mehtaheino/MANU-3D-Printer/Assets - Images for Documentation/0002-Accessories-100-1.jpg

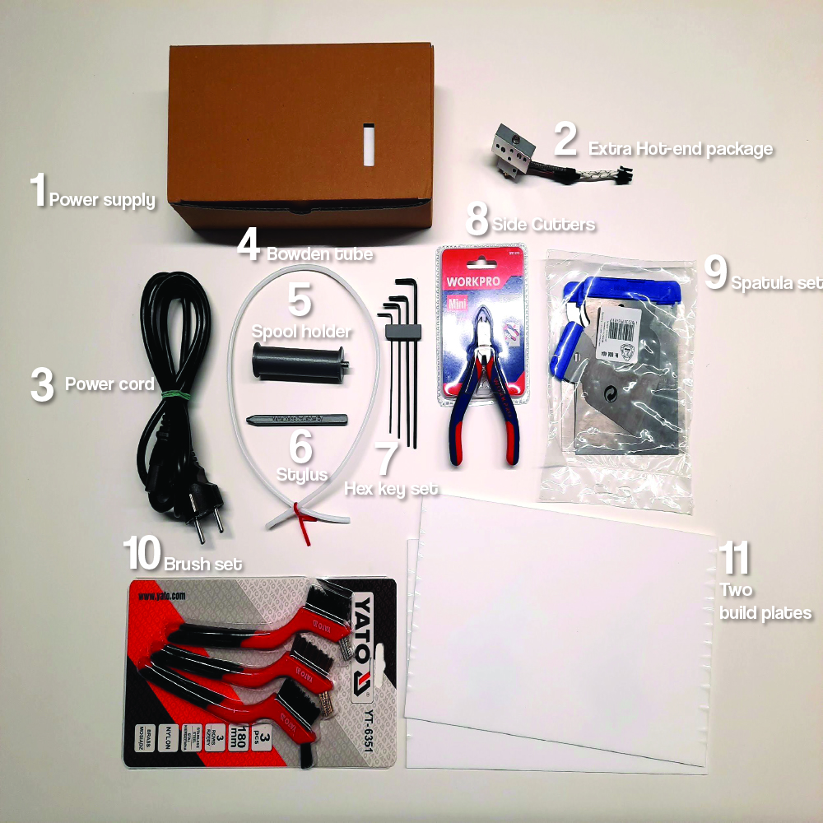
Assets - Images for Documentation/0002-Accessories-100-1.jpg
