mehtaheino/MANU-3D-Printer/Assets - Images for Documentation/About Creating STL files.png

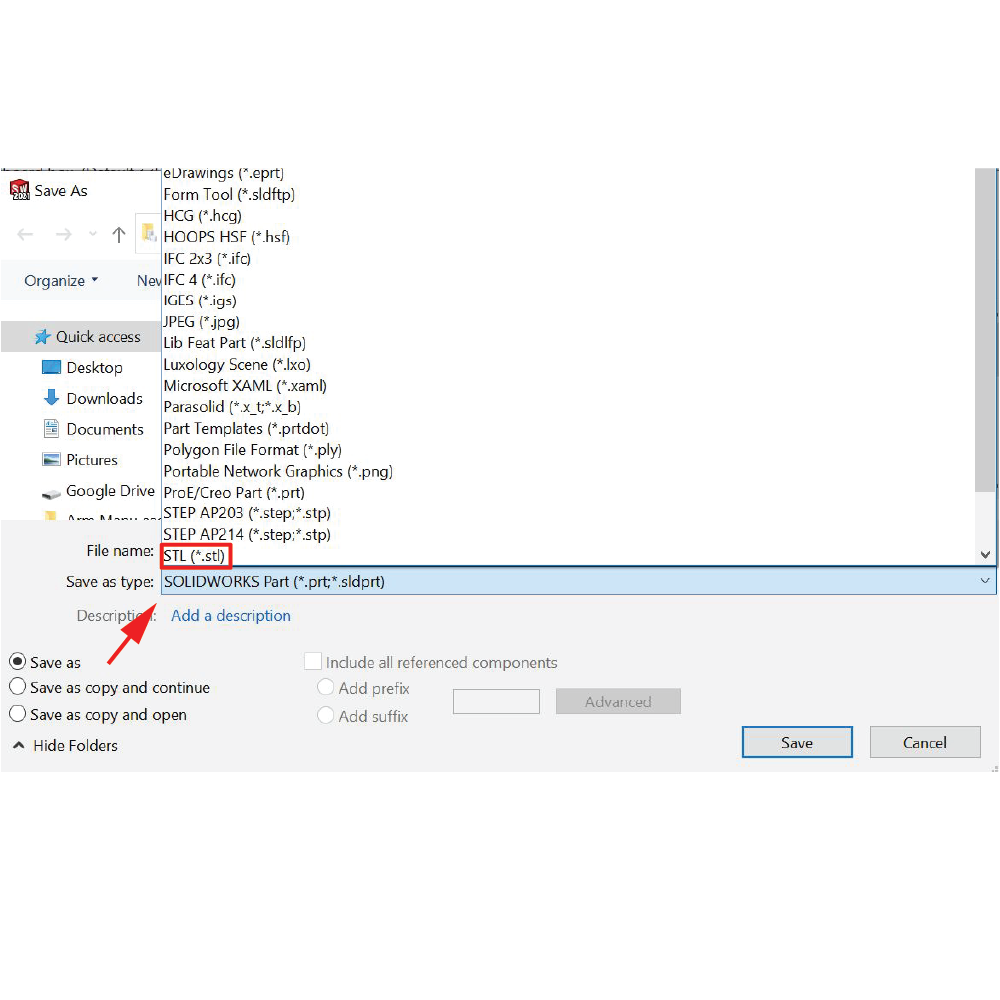
Assets - Images for Documentation/About Creating STL files.png
