mehtaheino/MANU-3D-Printer/Assets - Images for Documentation/Accessories.png

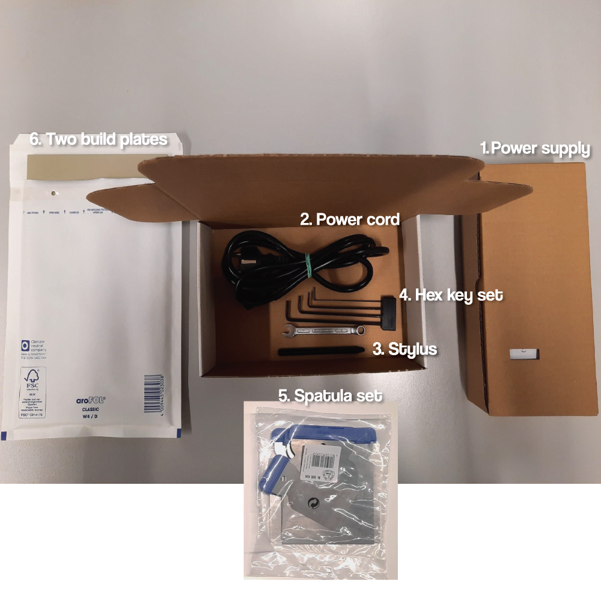
Assets - Images for Documentation/Accessories.png
