mehtaheino/MANU-3D-Printer/Assets - Images for Documentation/Choose the profile.png

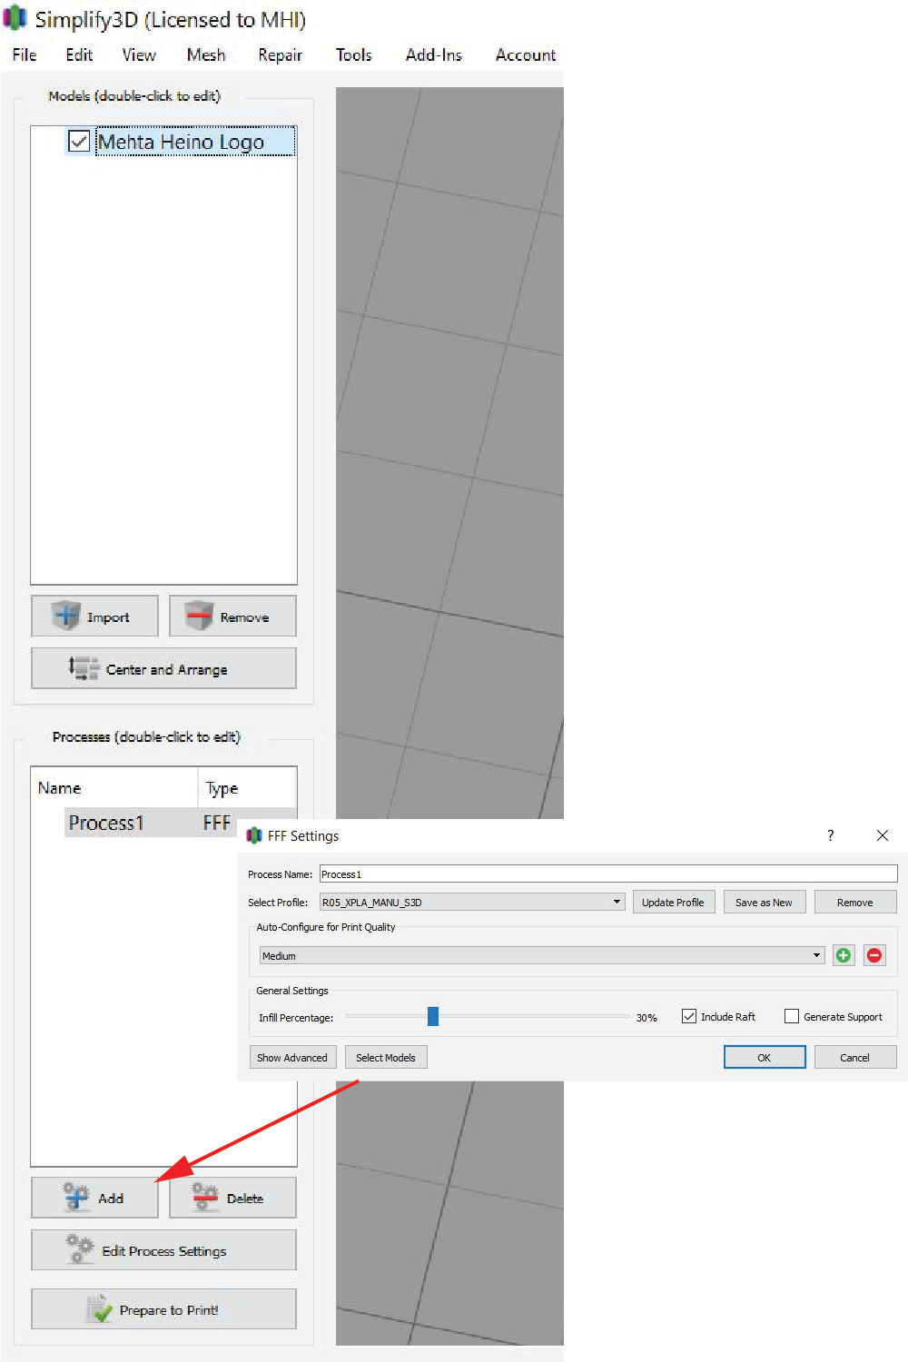
Assets - Images for Documentation/Choose the profile.png
