mehtaheino/MANU-3D-Printer/Assets - Images for Documentation/MEHTA-56--scaled.jpg

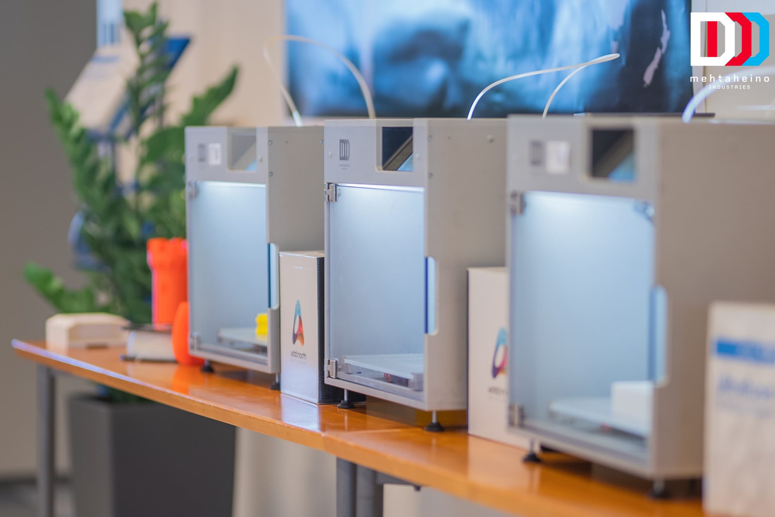
Assets - Images for Documentation/MEHTA-56--scaled.jpg
