mehtaheino/MANU-3D-Printer/Assets - Images for Documentation/MHE3D_00005.png

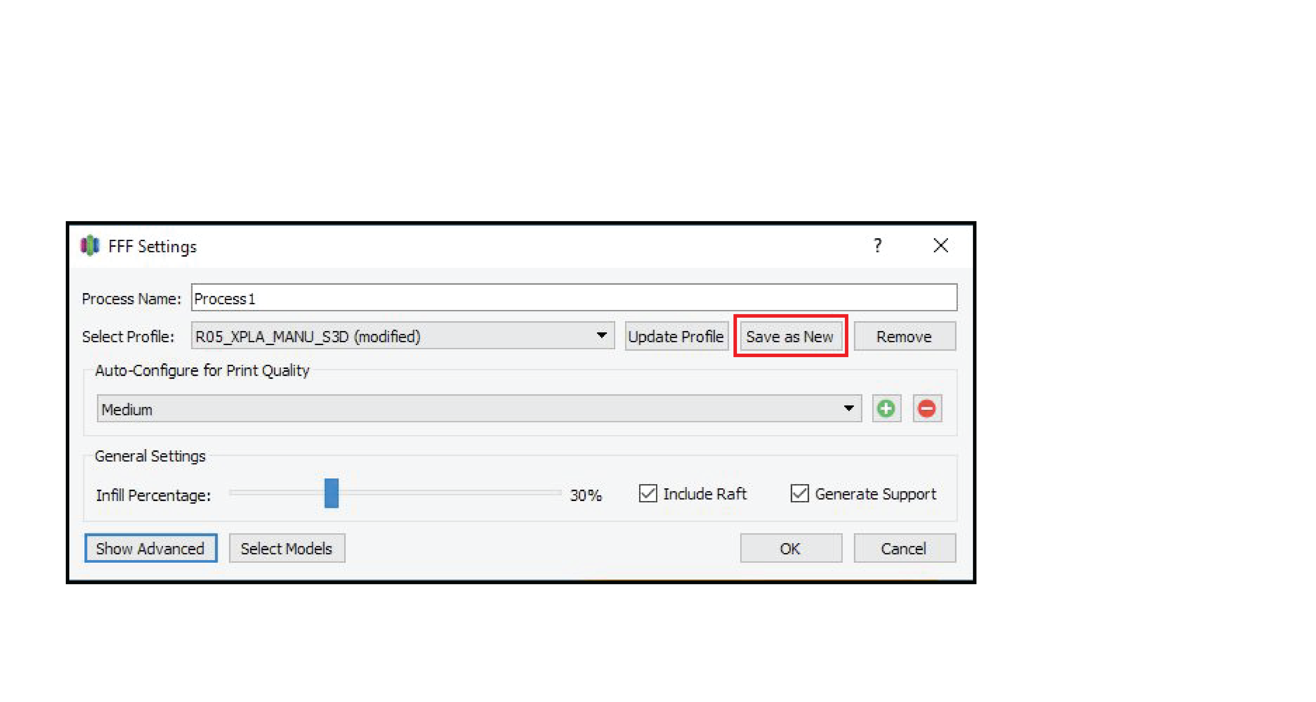
Assets - Images for Documentation/MHE3D_00005.png
