mehtaheino/MANU-3D-Printer/Assets - Images for Documentation/MHE3D_00037.jpg

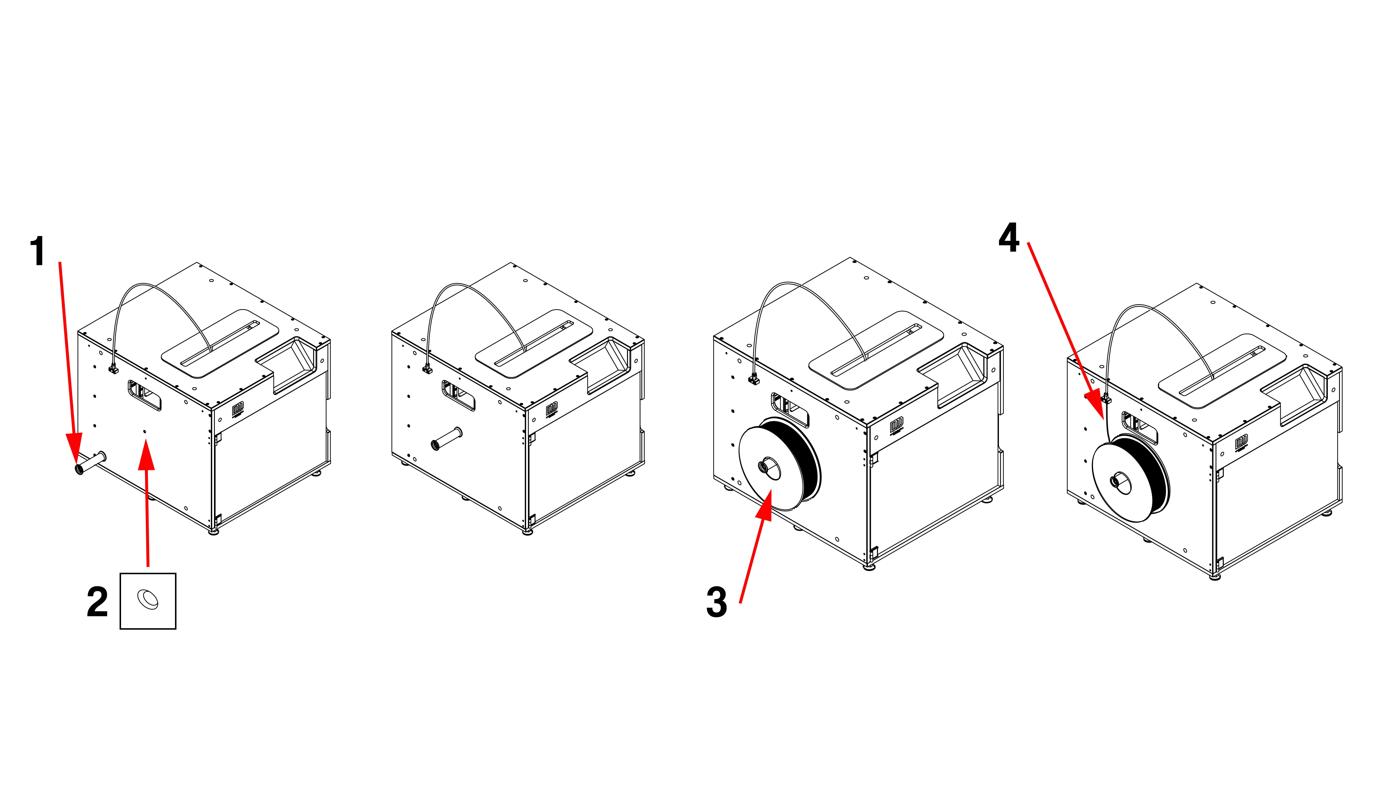
Assets - Images for Documentation/MHE3D_00037.jpg
