mehtaheino/MANU-3D-Printer/Assets - Images for Documentation/MHE3D_00043.jpg

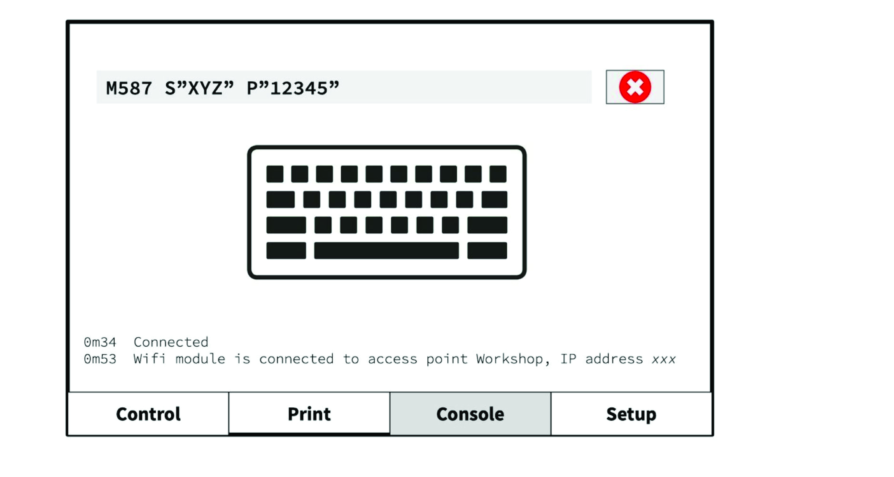
Assets - Images for Documentation/MHE3D_00043.jpg
