mehtaheino/MANU-3D-Printer/Assets - Images for Documentation/MHE3D_00059.png

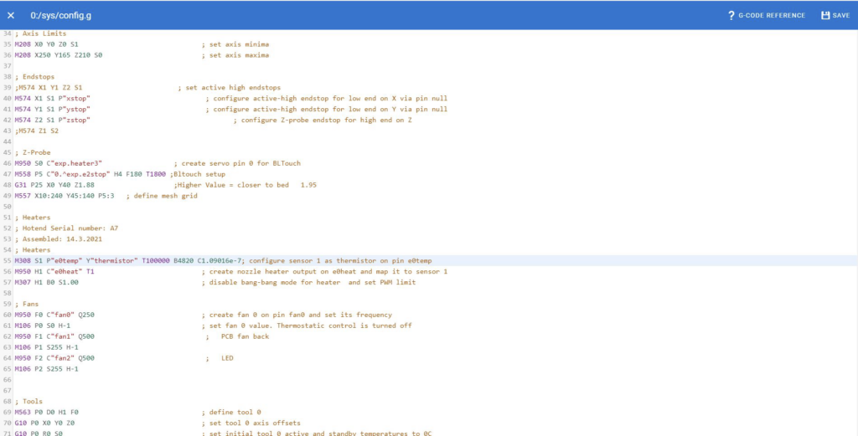
Assets - Images for Documentation/MHE3D_00059.png
