mehtaheino/MANU-3D-Printer/Assets - Images for Documentation/MHE3D_00060.png

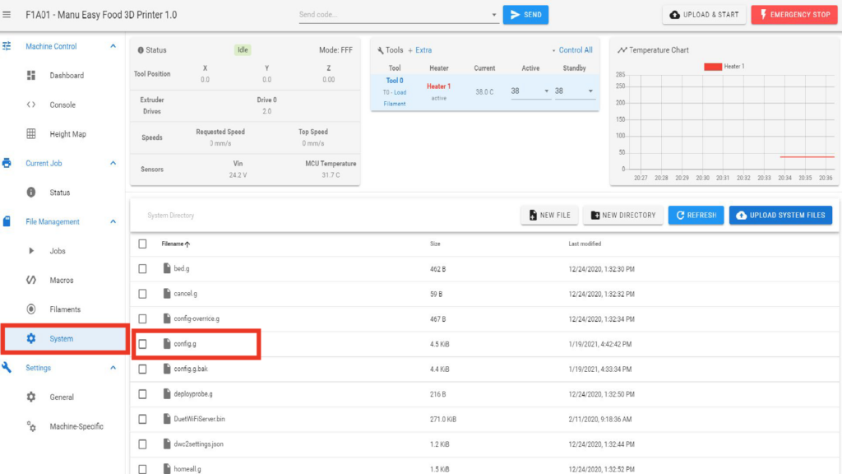
Assets - Images for Documentation/MHE3D_00060.png
