mehtaheino/MANU-3D-Printer/Assets - Images for Documentation/MHE3D_00066.jpg

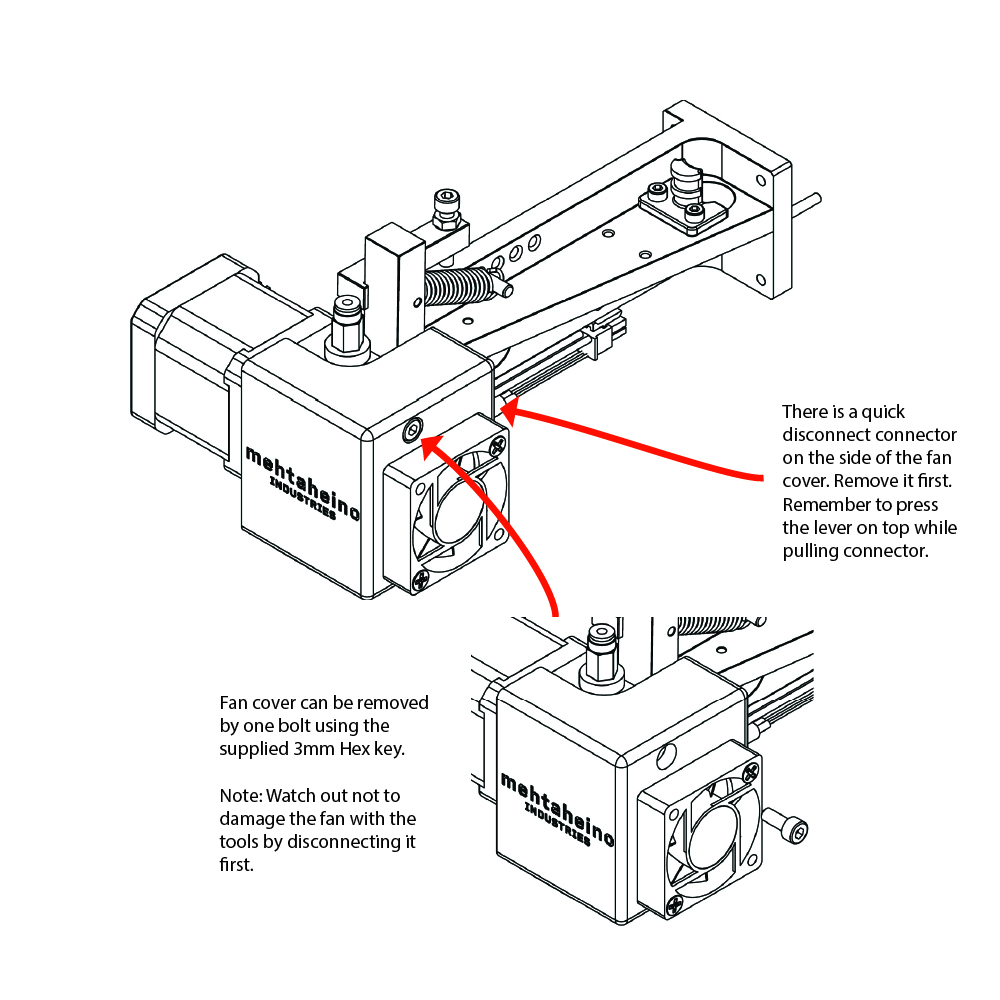
Assets - Images for Documentation/MHE3D_00066.jpg
