mehtaheino/MANU-3D-Printer/Assets - Images for Documentation/MHE3DP1Accessories.png

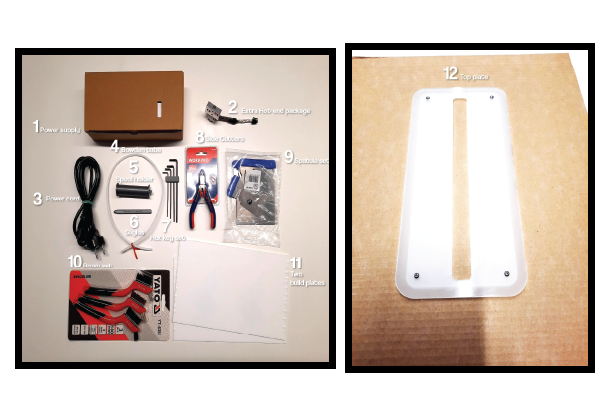
Assets - Images for Documentation/MHE3DP1Accessories.png
