mehtaheino/MANU-3D-Printer/Assets - Images for Documentation/MHE3DP1Opening the cardboard box.jpg

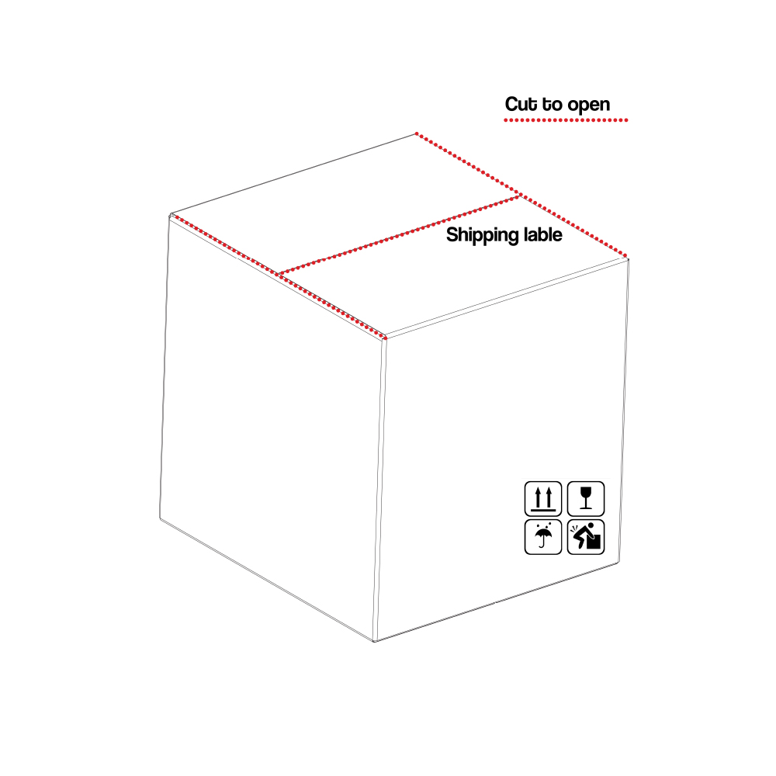
Assets - Images for Documentation/MHE3DP1Opening the cardboard box.jpg
