mehtaheino/MANU-3D-Printer/Assets - Images for Documentation/MHIME3D_00003.jpg

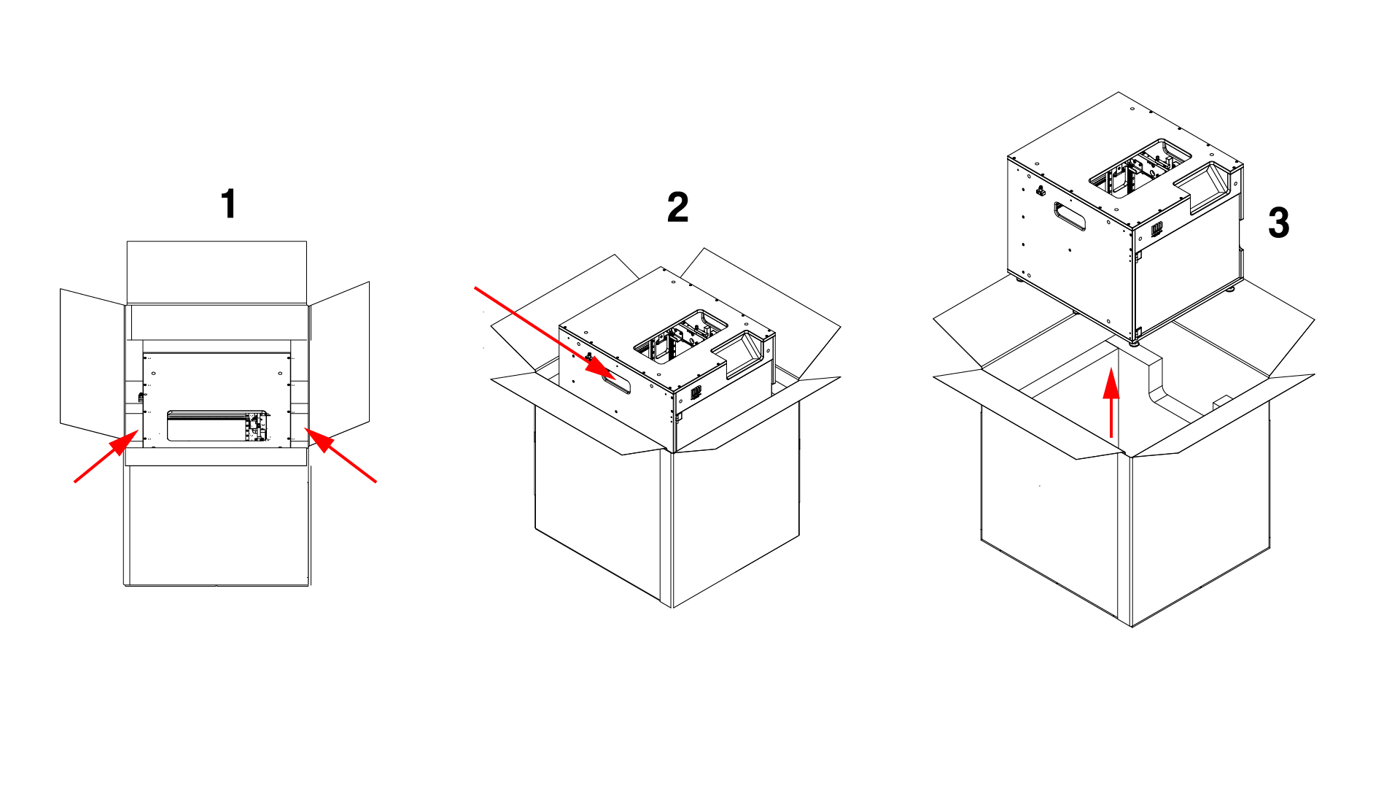
Assets - Images for Documentation/MHIME3D_00003.jpg
