mehtaheino/MANU-3D-Printer/Assets - Images for Documentation/MHIME3D_00008.jpg

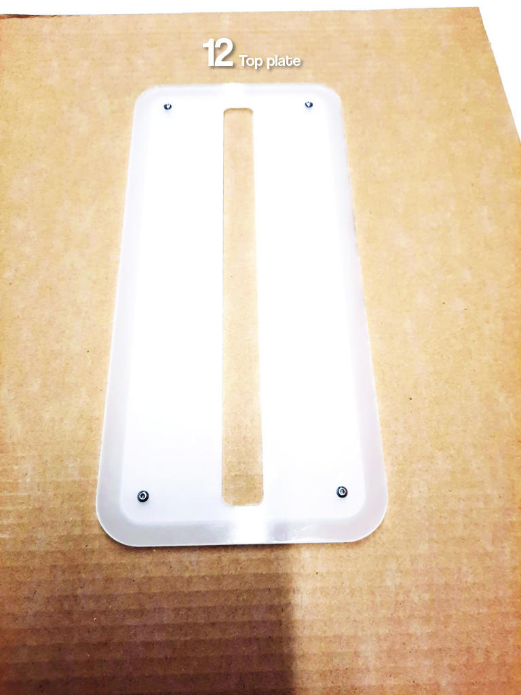
Assets - Images for Documentation/MHIME3D_00008.jpg
