mehtaheino/MANU-3D-Printer/Assets - Images for Documentation/OHMHE3DP1_Connecting first time.png

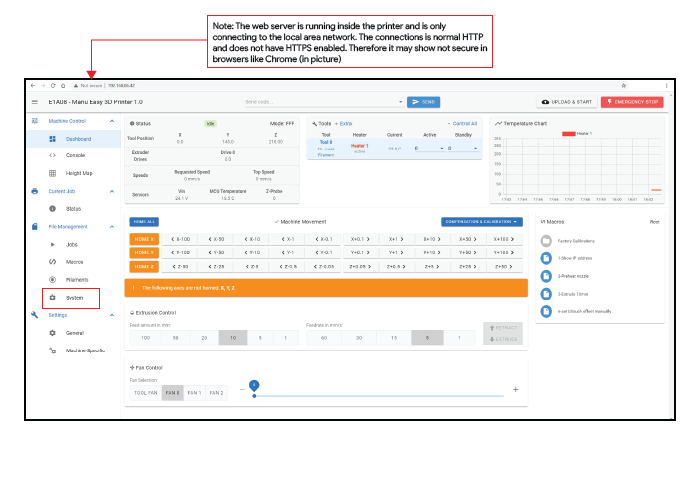
Assets - Images for Documentation/OHMHE3DP1_Connecting first time.png
