mehtaheino/MANU-3D-Printer/Assets - Images for Documentation/OHMHE3DP1_IAbout the slicing process.png

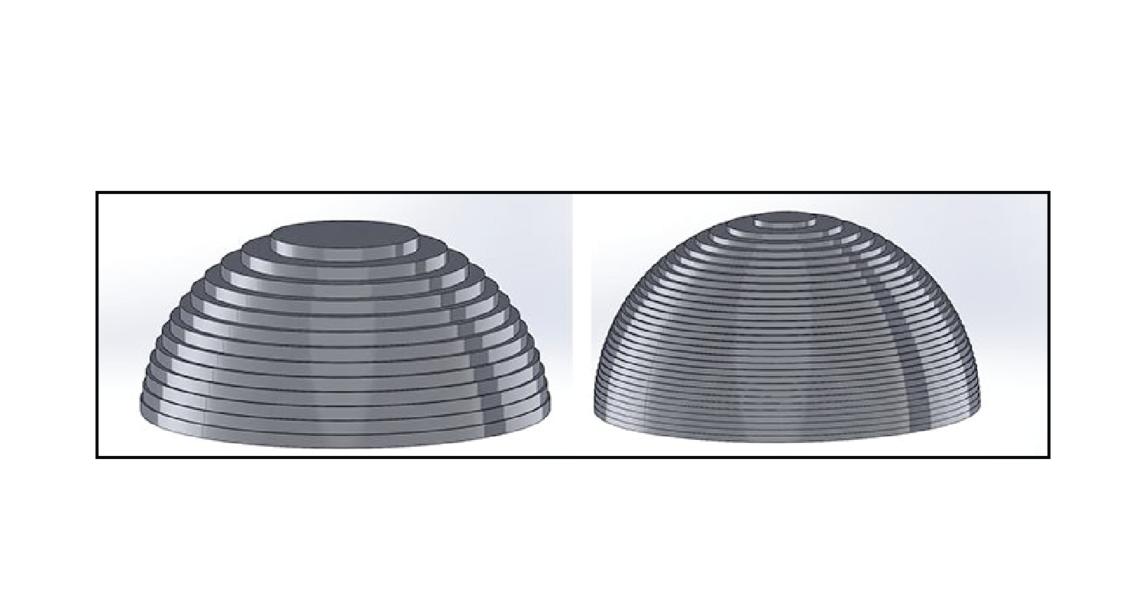
Assets - Images for Documentation/OHMHE3DP1_IAbout the slicing process.png
