mehtaheino/MANU-3D-Printer/Assets - Images for Documentation/OHMHE3DP1_Profile setting2.png

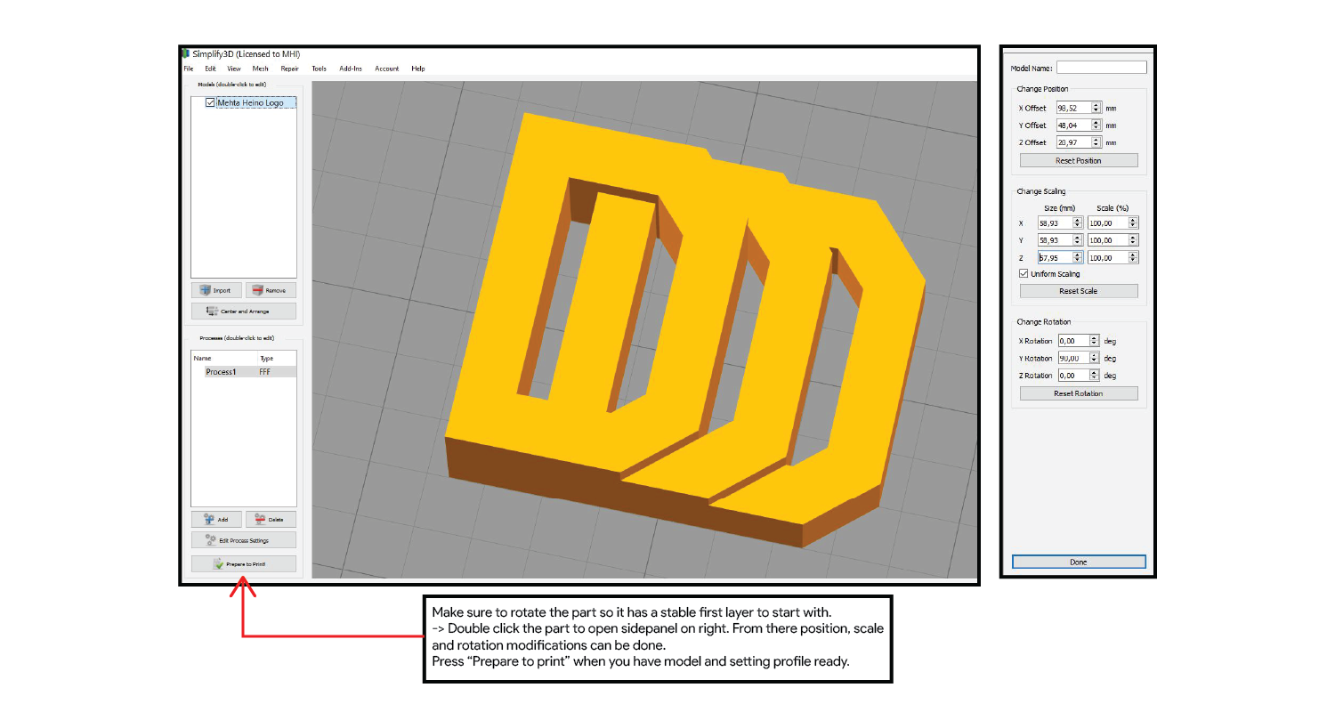
Assets - Images for Documentation/OHMHE3DP1_Profile setting2.png
