mehtaheino/MANU-3D-Printer/Assets - Images for Documentation/OHMHE3DP1Configuring the Wi-Fi.png

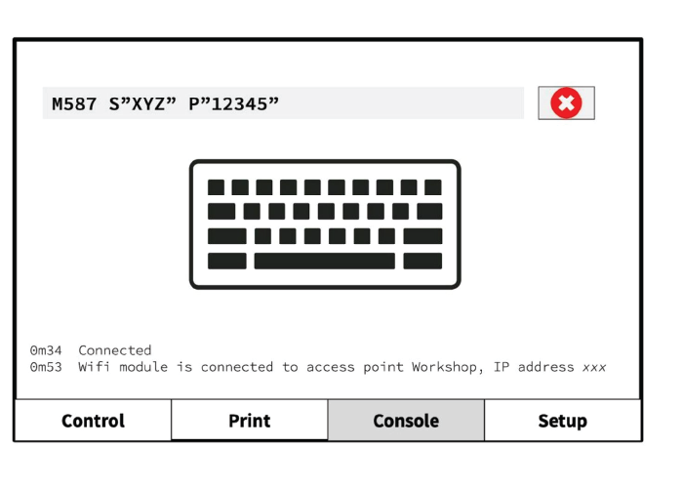
Assets - Images for Documentation/OHMHE3DP1Configuring the Wi-Fi.png
