mehtaheino/MANU-3D-Printer/Assets - Images for Documentation/OHMHE3DP1Connecting first time.png

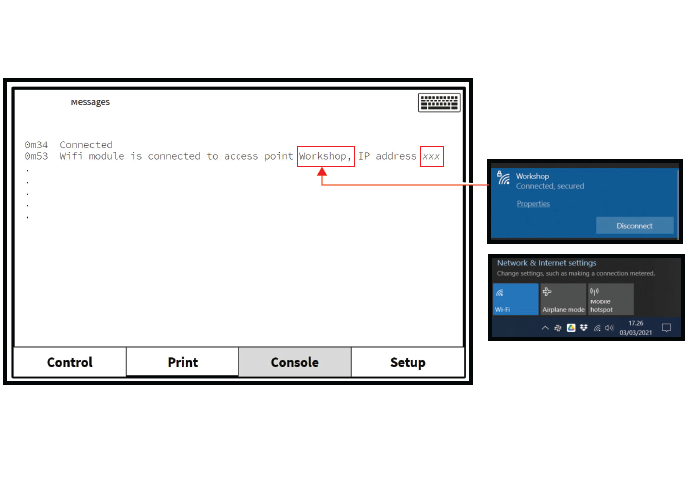
Assets - Images for Documentation/OHMHE3DP1Connecting first time.png
