mehtaheino/MANU-3D-Printer/Assets - Images for Documentation/OHMHE3DP1Info.png

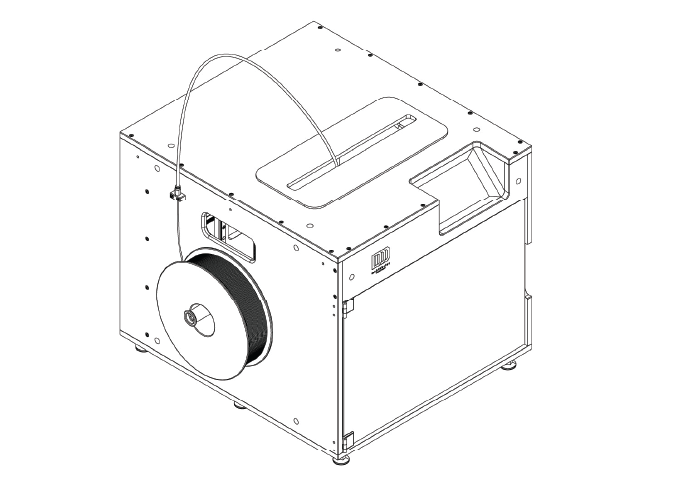
Assets - Images for Documentation/OHMHE3DP1Info.png
