mehtaheino/MANU-3D-Printer/Assets - Images for Documentation/Save g-code.png

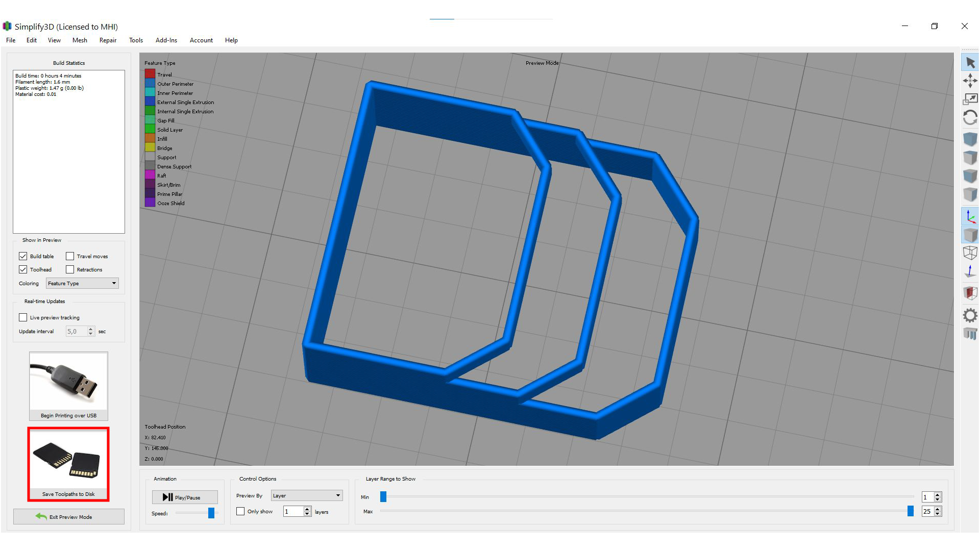
Assets - Images for Documentation/Save g-code.png
