mehtaheino/MANU-3D-Printer/Firmware on SD-Card - MANU E1/gcodes/cube - 6370662/images/56705f33-98fe-4adb-9f6f-353d322dd84d.png

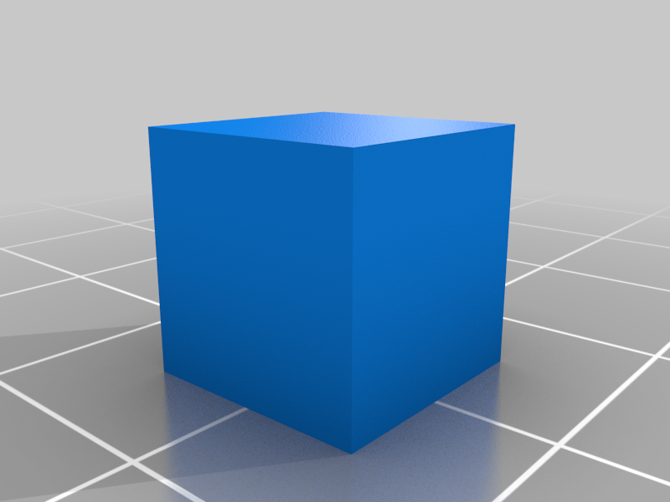
Firmware on SD-Card - MANU E1/gcodes/cube - 6370662/images/56705f33-98fe-4adb-9f6f-353d322dd84d.png
