mehtaheino/MANU-3D-Printer/Firmware on SD-Card - MANU E1/gcodes/Cylinder Compartment - 4225745/images/Cylinder_Compartments.png

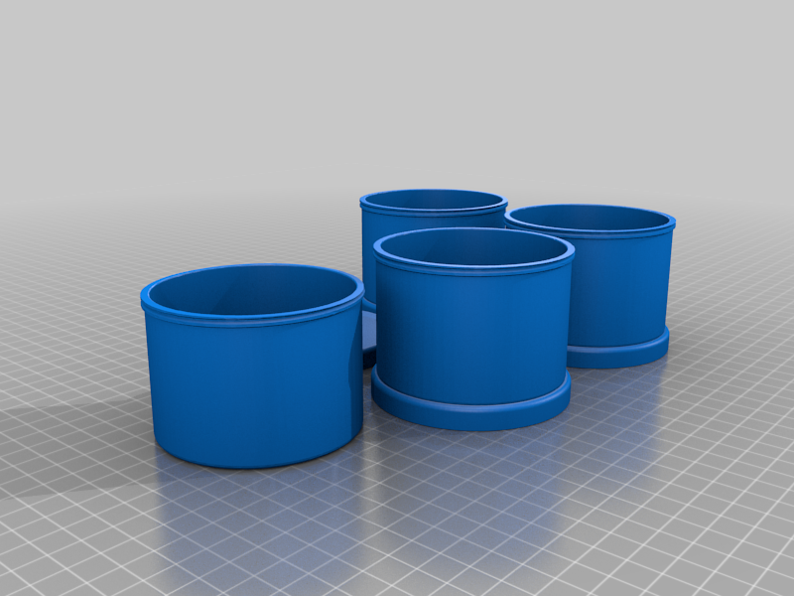
Firmware on SD-Card - MANU E1/gcodes/Cylinder Compartment - 4225745/images/Cylinder_Compartments.png
