mehtaheino/MANU-3D-Printer/Assets - Images for Documentation/Acrylic buildplate.png

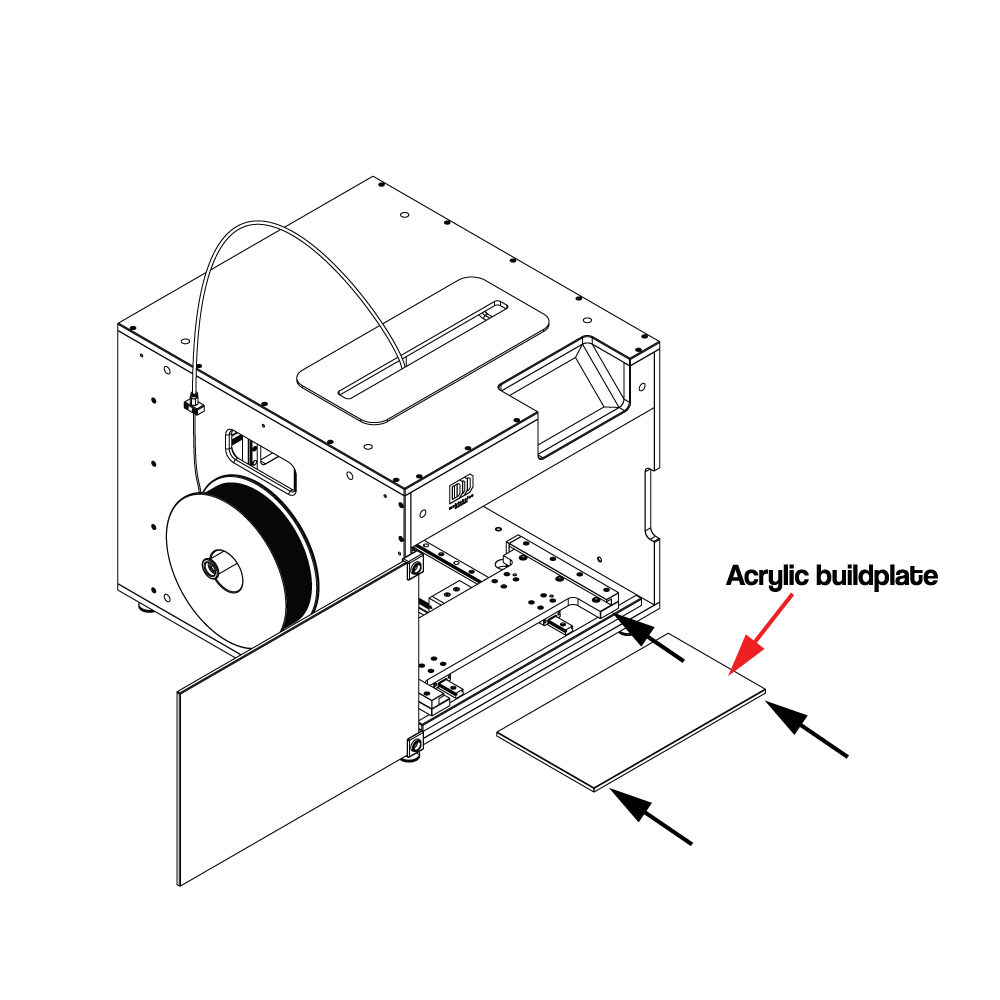
Assets - Images for Documentation/Acrylic buildplate.png
