mehtaheino/MANU-3D-Printer/Assets - Images for Documentation/Install Simplify3d.png

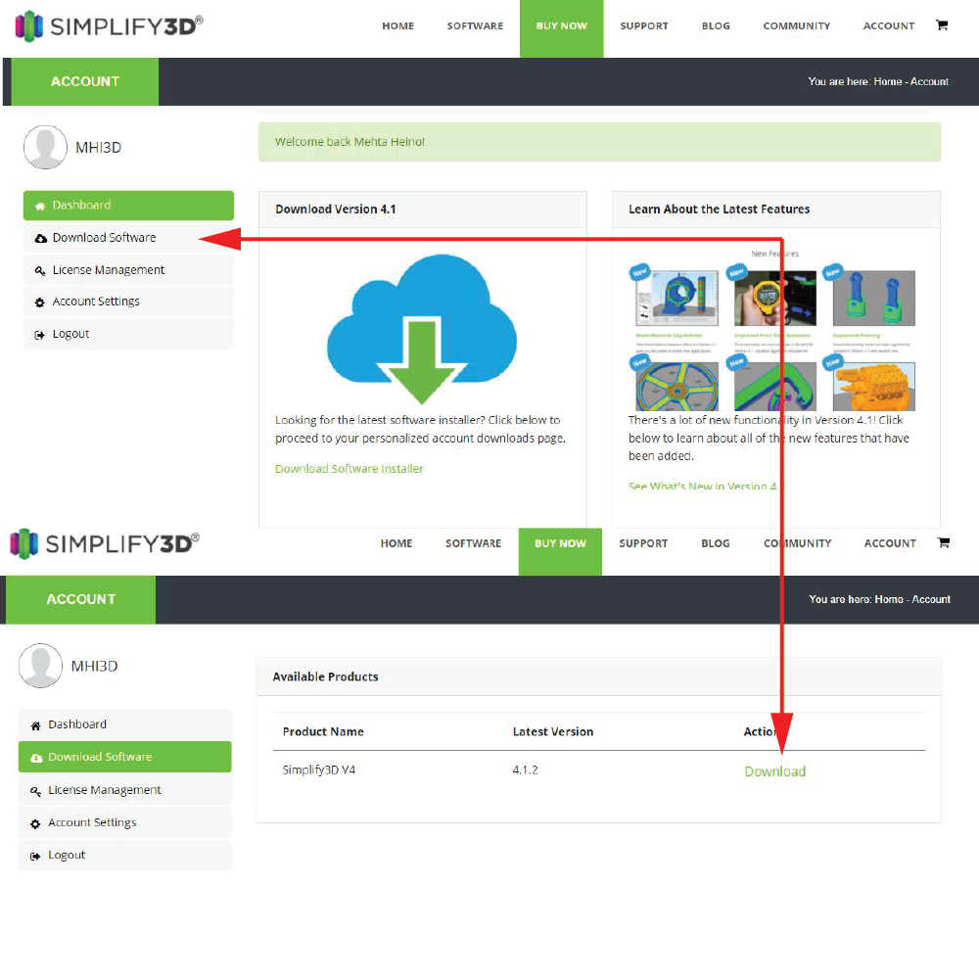
Assets - Images for Documentation/Install Simplify3d.png
