mehtaheino/MANU-3D-Printer/Assets - Images for Documentation/OHMHE3DP1_Insert the filament (Manually).png

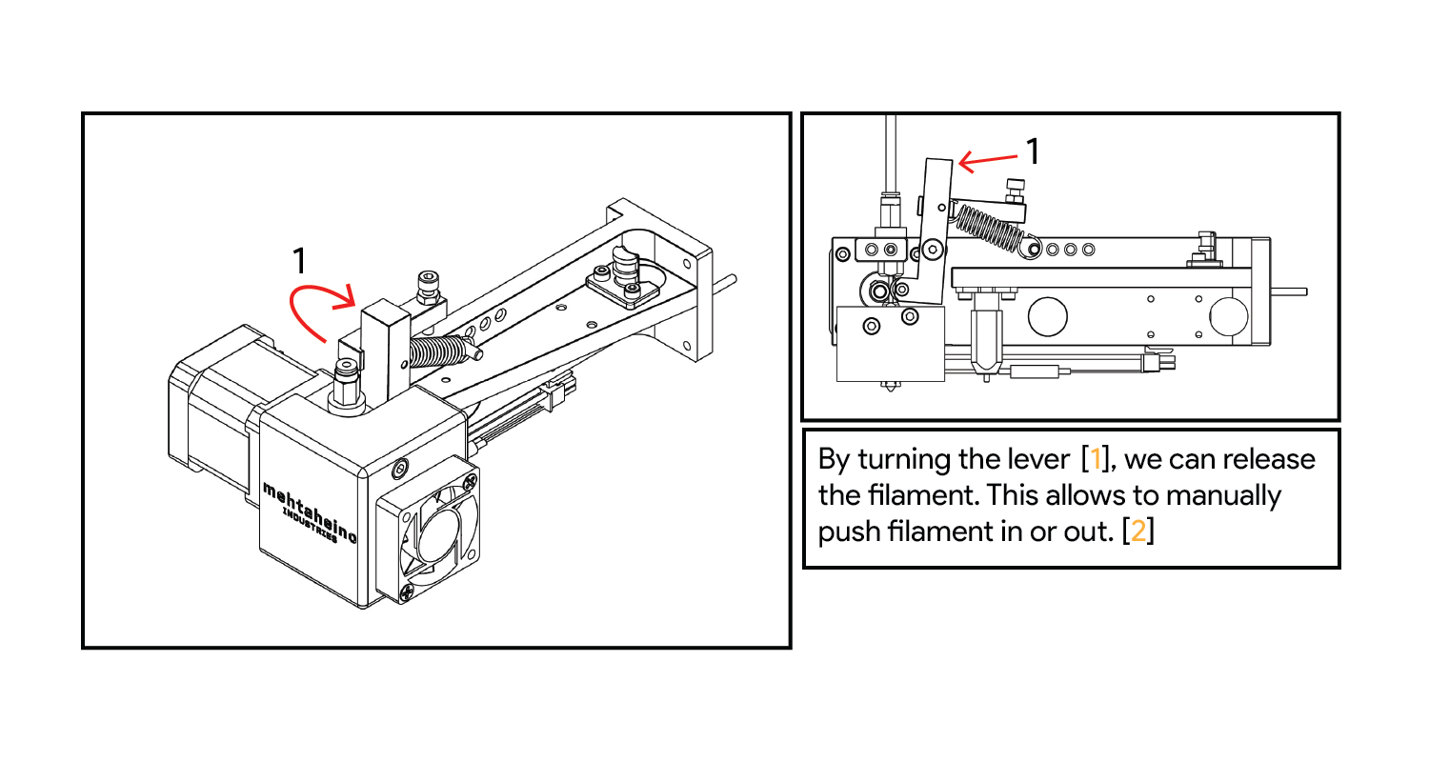
Assets - Images for Documentation/OHMHE3DP1_Insert the filament (Manually).png
