mehtaheino/MANU-3D-Printer/Assets - Images for Documentation/OHMHE3DP1_Recognizing build plate.png

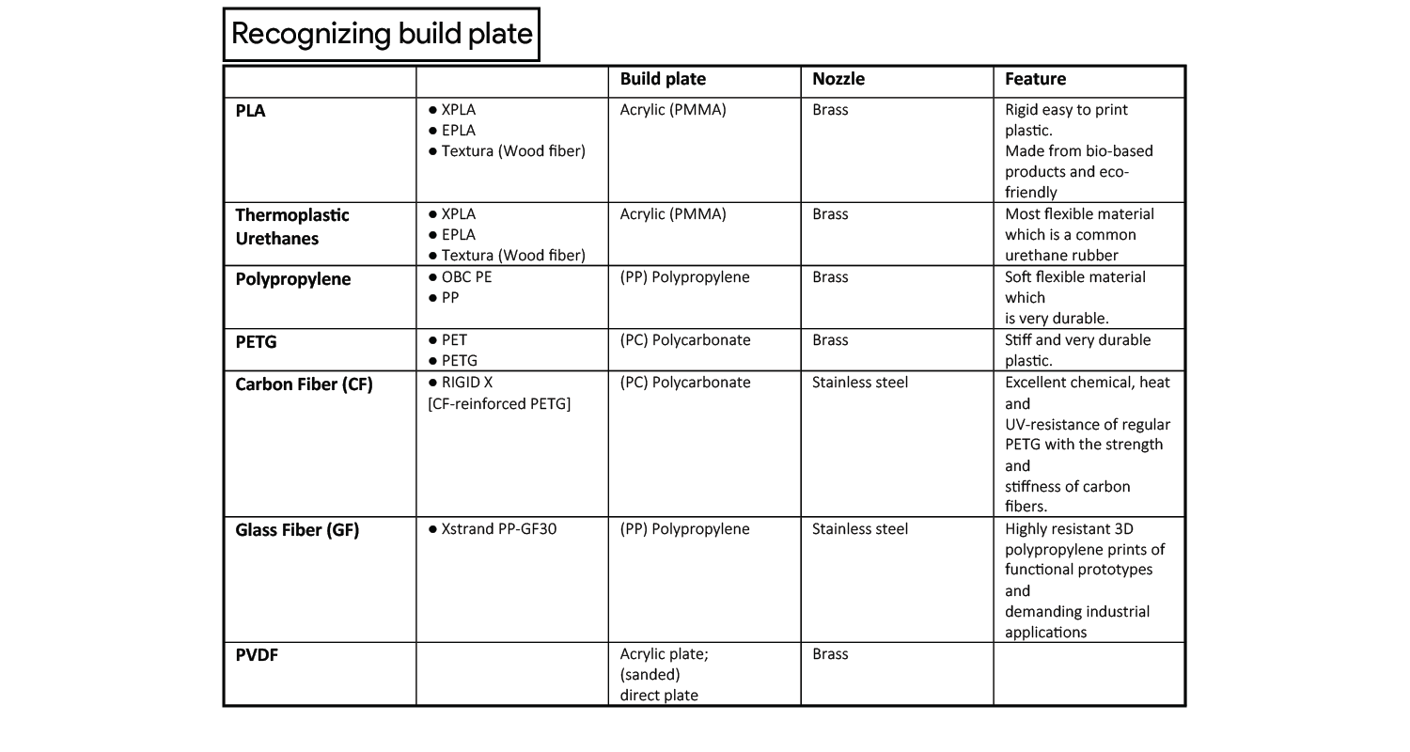
Assets - Images for Documentation/OHMHE3DP1_Recognizing build plate.png
