mehtaheino/MANU-3D-Printer/Assets - Images for Documentation/OHMHE3DP1Connecting the printer to Wi-Fi.png

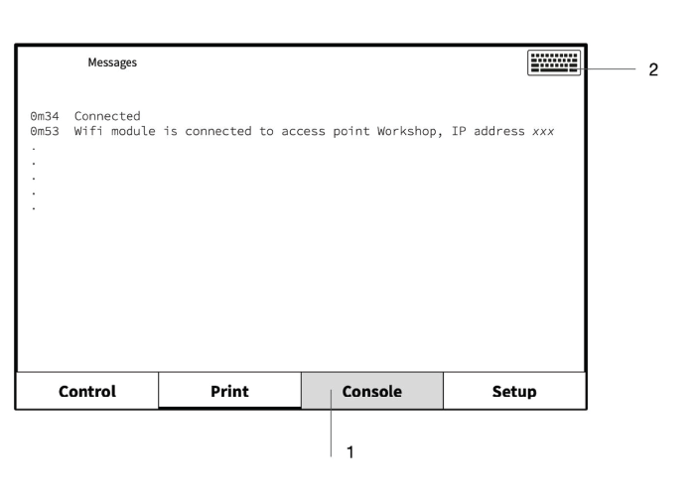
Assets - Images for Documentation/OHMHE3DP1Connecting the printer to Wi-Fi.png
