mehtaheino/MANU-3D-Printer/Simplify3D Print Settings - MANU E1/Addnorth E-PLA/Sample print for ANPL 1.0.0 E1 S3D/IMG_20220203_110758.jpg

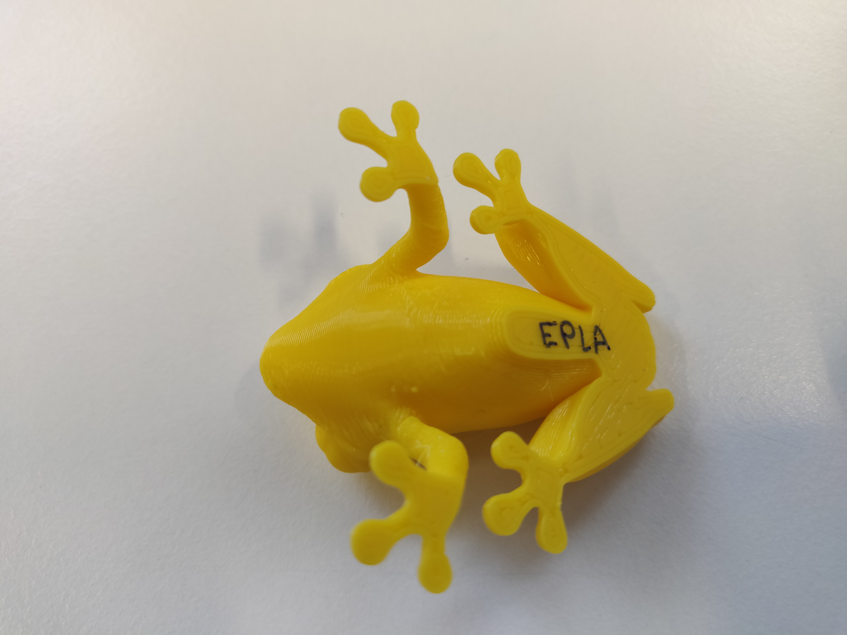
Simplify3D Print Settings - MANU E1/Addnorth E-PLA/Sample print for ANPL 1.0.0 E1 S3D/IMG_20220203_110758.jpg
