mehtaheino/MANU-3D-Printer/Simplify3D Print Settings - MANU E1/Addnorth Koltron G1/ANKG1-1.0.0-E1-S3D 21W30/Print’s Photos from ANKG1-0.1.0-E1-S3D profile 2021-07-29/WIN_20210730_11_26_26_Pro ANKG1-E1-S3D .jpg

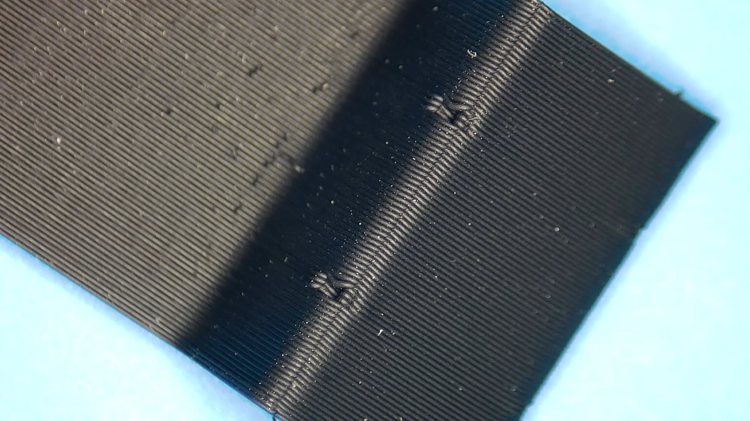
Simplify3D Print Settings - MANU E1/Addnorth Koltron G1/ANKG1-1.0.0-E1-S3D 21W30/Print’s Photos from ANKG1-0.1.0-E1-S3D profile 2021-07-29/WIN_20210730_11_26_26_Pro ANKG1-E1-S3D .jpg
