mehtaheino/MANU-3D-Printer/Simplify3D Print Settings - MANU E1/Addnorth OBC Polyethylene/Sample ANOB 1.0.0 E1 S3D/Screenshot 2021-11-10 135510.png

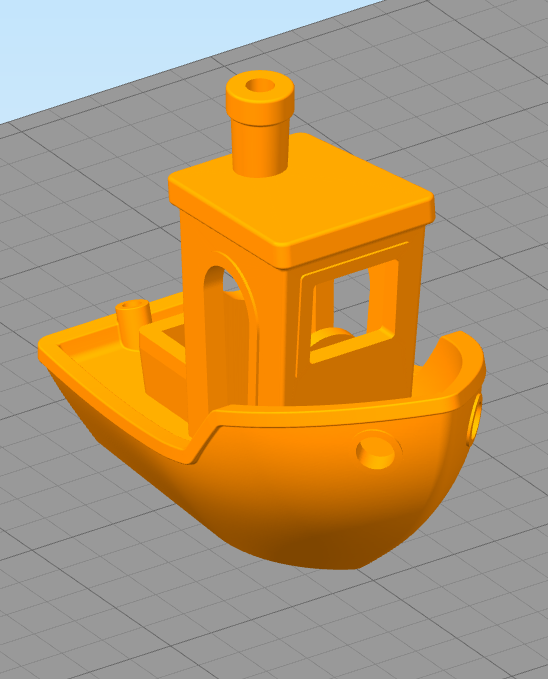
Simplify3D Print Settings - MANU E1/Addnorth OBC Polyethylene/Sample ANOB 1.0.0 E1 S3D/Screenshot 2021-11-10 135510.png
