mehtaheino/MANU-3D-Printer/Simplify3D Print Settings - MANU E1/Addnorth Textura/P100 Textura Addnorth/Textura P100 - IMG_0649.jpeg

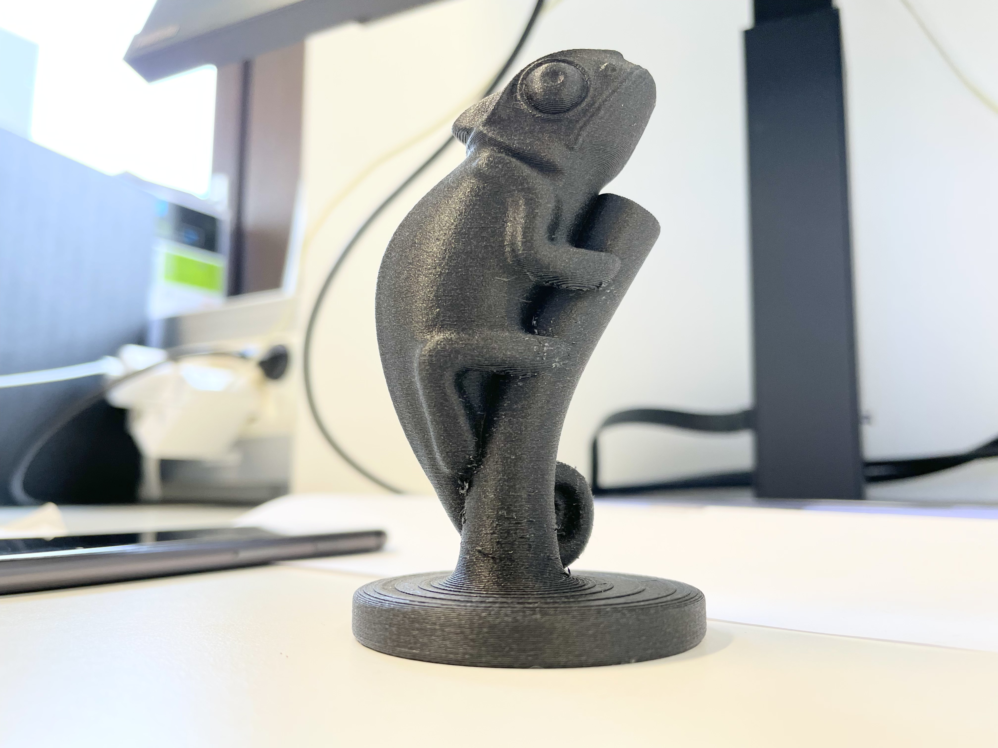
Simplify3D Print Settings - MANU E1/Addnorth Textura/P100 Textura Addnorth/Textura P100 - IMG_0649.jpeg
