mehtaheino/MANU-3D-Printer/Simplify3D Print Settings - MANU E1/Polymaker TPU-95/P87 Polymaker TPU-95/P87 TPU-95 IMG_0656.jpeg

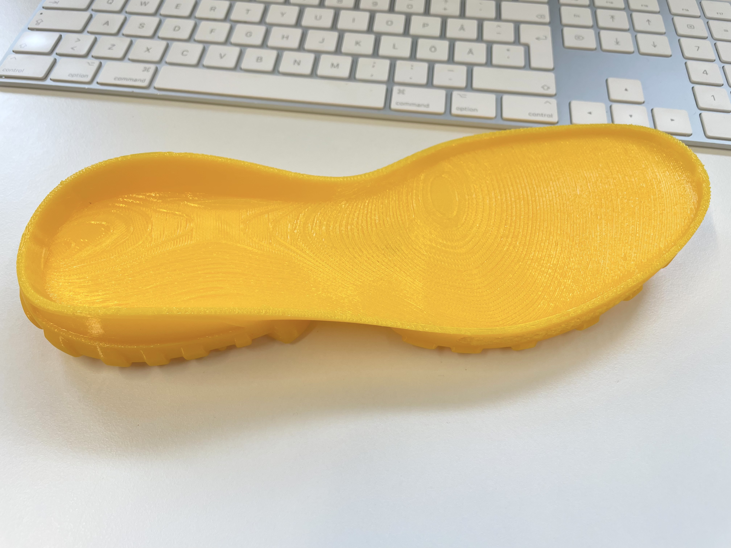
Simplify3D Print Settings - MANU E1/Polymaker TPU-95/P87 Polymaker TPU-95/P87 TPU-95 IMG_0656.jpeg
