mehtaheino/MANU-3D-Printer/Simplify3D Print Settings - MANU E1/Recreus TPU-60/FF60A 1.0.0 E1 S3D samples/P337 treefrog 45 cut.png

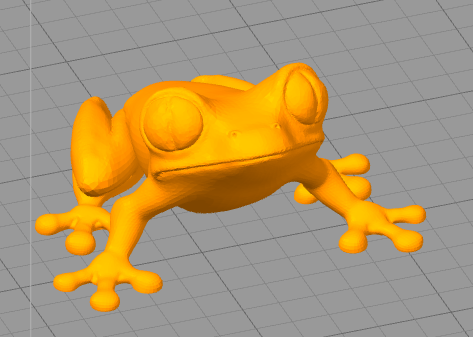
Simplify3D Print Settings - MANU E1/Recreus TPU-60/FF60A 1.0.0 E1 S3D samples/P337 treefrog 45 cut.png
