mehtaheino/MANU-3D-Printer/Simplify3D Print Settings - MANU E1/Ultrafuse TPS 90A/TPS 90A 1.0.0 sample/IMG_8723.jpg

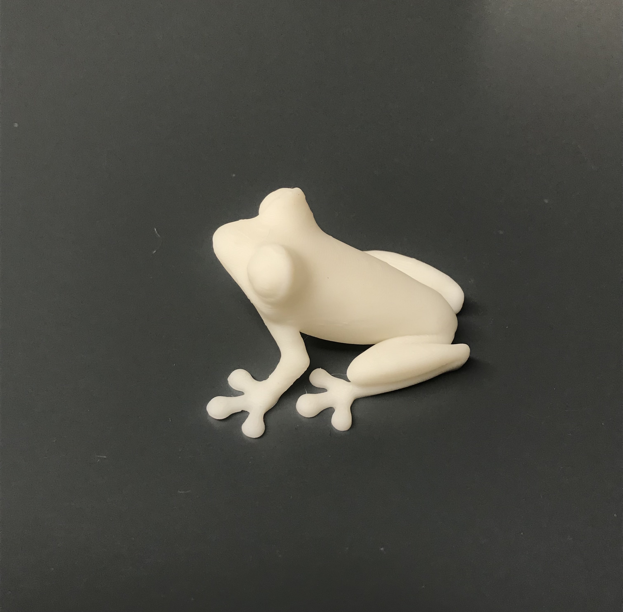
Simplify3D Print Settings - MANU E1/Ultrafuse TPS 90A/TPS 90A 1.0.0 sample/IMG_8723.jpg
